Freeman3389/RPI_Airbox/Docs/DSC_0648.JPG

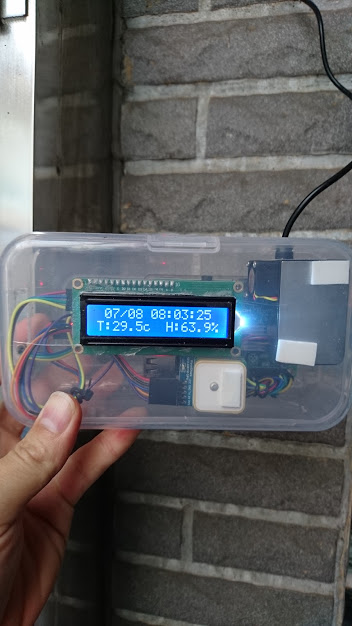
Docs/DSC_0648.JPG
